buntan-pc/buntan-pc/cpu/mcu_rev2.sv

// SPDX-License-Identifier: MIT
/*
 * Copyright (c) 2026 Kota UCHIDA
 */
`include "common.sv"

module mcu_rev2#(
  parameter CLOCK_HZ = 27_000_000,
  parameter UART_BAUD = 115200
) (
  input rst, clk, uart_rx, uart2_rx, uart3_rx,
  output uart_tx, uart2_tx, uart3_tx,
  output [`ADDR_WIDTH-1:0] dmem_addr,
  output dmem_wen, dmem_byt,
  input  [15:0] dmem_rdata_io, // メモリ読み込みデータ（IO 領域）
  output [15:0] dmem_wdata,    // メモリ書き込みデータ（全領域）
  output [17:0] uart_recv_data,
  output [`ADDR_WIDTH-1:0] img_pmem_size,
  input  clk125,
  output logic spk_on,// DAC をスピーカーへ接続するかどうかを制御
  input  adc_cmp,     // ADC のコンパレータ出力
  output adc_sh_on,   // ADC のサンプル&ホールドスイッチ制御
  output [2:0] adc_sel,  // ADC のチャンネル選択
  output [7:0] adc_vref, // ADC の DAC 入力
  output logic [8:0] uf_xadr,
  output logic [5:0] uf_yadr,
  output logic uf_xe, uf_ye, uf_se, uf_erase, uf_prog, uf_nvstr,
  output logic [31:0] uf_din,
  input  [31:0] uf_dout,
  output spi_cs,
  output spi_sclk, spi_mosi,
  input  spi_miso,
  inout  i2c_scl, i2c_sda
);

localparam DMEM_GVAR_START = `ADDR_WIDTH'h0100;
localparam KEY_ROW_FOR_DEBUG = 0;
localparam KEY_COL_FOR_DEBUG = 0;

// CPU コア
logic [`ADDR_WIDTH-1:0] cpu_dmem_addr, cpu_dmem_addr_d, cpu_pmem_addr, pmem_addr;
logic [15:0] cpu_dmem_rdata, cpu_dmem_wdata;
logic [17:0] cpu_pmem_rdata, cpu_pmem_wdata;
logic cpu_dmem_ren, cpu_dmem_wen, cpu_dmem_byt, cpu_irq;
logic cpu_rst, cpu_pmem_wenh, cpu_pmem_wenl, pmem_wenh, pmem_wenl;

logic [17:0] recv_data, pmem_wdata;
logic [`ADDR_WIDTH-1:0] img_recv_addr, pmem_size, dmem_size;
logic [15:0] dmem_rdata_mem, dmem_rdata_mem_d;

assign uart_recv_data = recv_data;
assign img_pmem_size = pmem_size;

typedef enum logic [2:0] {
  IMG_RECV_WAIT, // メモリイメージ受信開始（55 AA）を待っている
  IMG_RECV_META, // メタデータ（データサイズなど）受信中
  IMG_RECV_PMEM, // pmem 受信中
  IMG_RECV_DMEM, // dmem 受信中
  IMG_RECV_FIN   // 終了処理
} img_recv_state_t;
img_recv_state_t img_recv_state;

// 0: 最上位バイトを待っている
// 2: 最下位バイトを待っている
logic [1:0] recv_byte_phase;

logic recv_data_v, recv_compl, uart_rx_ready;

//localparam CLK_DIV = 27_000_000 << 1;
//localparam CLK_DIV = 27_000_000 >> 1;
//localparam CLK_DIV = 27_000_000;
localparam CLK_DIV = 1;
logic [25:0] clk_div_cnt;
logic clk_div, cpu_clk;

always @(posedge rst, posedge clk) begin
  if (rst)
    clk_div_cnt <= 0;
  else if (clk_div_cnt == CLK_DIV - 1)
    clk_div_cnt <= 0;
  else
    clk_div_cnt <= clk_div_cnt + 1;
end

always @(posedge rst, posedge clk) begin
  if (rst)
    clk_div <= 0;
  else if (clk_div_cnt == CLK_DIV - 1)
    clk_div <= 0;
  else if (clk_div_cnt == (CLK_DIV >> 1))
    clk_div <= 1;
end

always @(posedge rst, posedge clk) begin
  if (rst)
    dmem_rdata_mem_d <= 0;
  else if (clk_div_cnt == (CLK_DIV >> 1) + 1)
    dmem_rdata_mem_d <= dmem_rdata_mem;
end

assign cpu_clk = CLK_DIV >= 2 ? clk_div : clk;
assign cpu_rst = rst | ~recv_compl;

always @(posedge cpu_clk, posedge rst) begin
  if (rst)
    cpu_dmem_addr_d <= `ADDR_WIDTH'd0;
  else
    cpu_dmem_addr_d <= cpu_dmem_addr;
end

cpu#(.CLOCK_HZ(CLOCK_HZ)) cpu(
  .rst(cpu_rst),
  .clk(cpu_clk),
  .irq(cpu_irq),
  .dmem_ren(cpu_dmem_ren),
  .dmem_wen(cpu_dmem_wen),
  .dmem_byt(cpu_dmem_byt),
  .dmem_addr(cpu_dmem_addr),
  .dmem_rdata(cpu_dmem_rdata),
  .dmem_wdata(cpu_dmem_wdata),
  .pmem_wenh(cpu_pmem_wenh),
  .pmem_wenl(cpu_pmem_wenl),
  .pmem_addr(cpu_pmem_addr),
  .pmem_rdata(cpu_pmem_rdata),
  .pmem_wdata(cpu_pmem_wdata)
);

// データメモリ
dmem dmem(
  .rst(rst),
  .clk(clk),
  .addr(dmem_addr),
  .wen(dmem_wen),
  .byt(dmem_byt),
  .data_in(dmem_wdata),
  .data_out(dmem_rdata_mem)
);

// プログラムメモリ
pmem pmem(
  .rst(rst),
  .clk(clk),
  .addr(pmem_addr),
  .wenh(pmem_wenh),
  .wenl(pmem_wenl),
  .data_in(pmem_wdata),
  .data_out(cpu_pmem_rdata)
);

// MCU 内蔵周辺機能：カウントダウンタイマ
logic cdtimer_to, load_cdtimer, cdtimer_ie;
logic [15:0] data_memreg, data_reg, cdtimer_cnt;

cdtimer#(.PERIOD(CLOCK_HZ/1000)) cdtimer(
  .rst(cpu_rst),
  .clk(clk),
  .load(load_cdtimer),
  .data(dmem_wdata),
  .counter(cdtimer_cnt),
  .timeout(cdtimer_to)
);

assign load_cdtimer = cpu_dmem_wen & cpu_dmem_addr === `ADDR_WIDTH'h002;

always @(posedge clk, posedge cpu_rst) begin
  if (cpu_rst)
    cdtimer_ie <= 1'b0;
  else if (cpu_dmem_wen && cpu_dmem_addr === `ADDR_WIDTH'h004)
    cdtimer_ie <= cpu_dmem_wdata[1];
end

// MCU 内蔵周辺機能：UART
logic [7:0] uart_rx_byte, uart_tx_byte;
logic uart_rd, uart_rx_full, uart_wr, uart_tx_ready, uart_ie;
logic img_recv, end_img_recv;

uart_mux#(.CLOCK_HZ(CLOCK_HZ), .BAUD(UART_BAUD), .TIM_WIDTH(8)) uart_mux(
  .rst(rst),
  .clk(clk),
  .rx(uart_rx),
  .tx(uart_tx),
  .rx_data(uart_rx_byte),
  .tx_data(uart_tx_byte),
  .rd(uart_rd),
  .rx_full(uart_rx_full),
  .wr(uart_wr),
  .tx_ready(uart_tx_ready),
  .img_recv(img_recv),
  .end_img_recv(end_img_recv)
);

assign uart_rd = uart_rx_full;
assign uart_wr = cpu_dmem_wen & cpu_dmem_addr === `ADDR_WIDTH'h006;
assign uart_tx_byte = cpu_dmem_wdata[7:0];
assign end_img_recv = img_recv_state == IMG_RECV_FIN;

always @(posedge clk, posedge rst) begin
  if (rst)
    uart_ie <= 1'b0;
  else if (cpu_dmem_wen && cpu_dmem_addr === `ADDR_WIDTH'h008)
    uart_ie <= cpu_dmem_wdata[1];
end

// MCU 内蔵周辺機能：UART2
logic [7:0] uart2_rx_byte, uart2_tx_byte;
logic uart2_rd, uart2_rx_full, uart2_wr, uart2_tx_ready, uart2_ie;

uart#(.CLOCK_HZ(CLOCK_HZ), .BAUD(9600), .TIM_WIDTH(12)) uart2(
  .rst(rst),
  .clk(clk),
  .rx(uart2_rx),
  .tx(uart2_tx),
  .rx_data(uart2_rx_byte),
  .tx_data(uart2_tx_byte),
  .rd(uart2_rd),
  .rx_full(uart2_rx_full),
  .wr(uart2_wr),
  .tx_ready(uart2_tx_ready)
);

assign uart2_rd = cpu_dmem_ren & cpu_dmem_addr_d === `ADDR_WIDTH'h02C;
assign uart2_wr = cpu_dmem_wen & cpu_dmem_addr === `ADDR_WIDTH'h02C;
assign uart2_tx_byte = cpu_dmem_wdata[7:0];

always @(posedge clk, posedge rst) begin
  if (rst)
    uart2_ie <= 1'b0;
  else if (cpu_dmem_wen && cpu_dmem_addr === `ADDR_WIDTH'h02E)
    uart2_ie <= cpu_dmem_wdata[1];
end

// MCU 内蔵周辺機能：UART3
logic [7:0] uart3_rx_byte, uart3_tx_byte;
logic uart3_rd, uart3_rx_full, uart3_wr, uart3_tx_ready, uart3_ie;

uart#(.CLOCK_HZ(CLOCK_HZ), .BAUD(9600), .TIM_WIDTH(12)) uart3(
  .rst(rst),
  .clk(clk),
  .rx(uart3_rx),
  .tx(uart3_tx),
  .rx_data(uart3_rx_byte),
  .tx_data(uart3_tx_byte),
  .rd(uart3_rd),
  .rx_full(uart3_rx_full),
  .wr(uart3_wr),
  .tx_ready(uart3_tx_ready)
);

assign uart3_rd = cpu_dmem_ren & cpu_dmem_addr_d === `ADDR_WIDTH'h030;
assign uart3_wr = cpu_dmem_wen & cpu_dmem_addr === `ADDR_WIDTH'h030;
assign uart3_tx_byte = cpu_dmem_wdata[7:0];

always @(posedge clk, posedge rst) begin
  if (rst)
    uart3_ie <= 1'b0;
  else if (cpu_dmem_wen && cpu_dmem_addr === `ADDR_WIDTH'h02E)
    uart3_ie <= cpu_dmem_wdata[1];
end

// MCU 内蔵周辺機能：ADC
logic [7:0] adc_result;
logic [7:0] vref_for_adc, vref_for_spk;
logic en_adc; // ADC 有効化（無効状態では DAC がスピーカー用になる）

adc_rev2#(.CLOCK_HZ(CLOCK_HZ)) adc(
  .rst(rst),
  .clk(clk),
  .clk125(clk125),
  .adc_cmp(adc_cmp),
  .adc_sh_on(adc_sh_on),
  .adc_sel(adc_sel),
  .adc_vref(vref_for_adc),
  .adc_result(adc_result)
);

assign adc_vref = en_adc ? vref_for_adc : vref_for_spk;

always @(posedge clk, posedge rst) begin
  if (rst) begin
    en_adc <= 1'b1;
    spk_on <= 1'b0;
  end
  else if (cpu_dmem_wen && cpu_dmem_addr === `ADDR_WIDTH'h00C) begin
    vref_for_spk <= cpu_dmem_wdata[7:0];
    en_adc <= cpu_dmem_wdata[8];
    spk_on <= cpu_dmem_wdata[9];
  end
end

// MCU 内蔵周辺機能：ユーザーフラッシュ
always @(posedge clk, posedge cpu_rst) begin
  if (cpu_rst) begin
    uf_xadr <= 0;
    uf_yadr <= 0;
    {uf_nvstr, uf_prog, uf_erase, uf_se, uf_ye, uf_xe} <= 0;
    uf_din <= 0;
  end
  else if (cpu_dmem_wen)
    case (cpu_dmem_addr)
      `ADDR_WIDTH'h010: uf_xadr <= cpu_dmem_wdata[8:0];
      `ADDR_WIDTH'h012: uf_yadr <= cpu_dmem_wdata[5:0];
      `ADDR_WIDTH'h014: {uf_nvstr, uf_prog, uf_erase, uf_se, uf_ye, uf_xe} <= cpu_dmem_wdata[5:0];
      `ADDR_WIDTH'h018: uf_din[15:0] <= cpu_dmem_wdata;
      `ADDR_WIDTH'h01A: uf_din[31:16] <= cpu_dmem_wdata;
      `ADDR_WIDTH'h01C: ; // cannot write to df_uout
      `ADDR_WIDTH'h01E: ; // cannot write to df_uout
    endcase
end

// MCU 内蔵周辺機能：SPI
logic spi_tx_start, spi_tx_ready, spi_cs_reg;
logic [7:0] spi_rx_data;

assign spi_tx_start = cpu_dmem_wen & cpu_dmem_addr === `ADDR_WIDTH'h020;
assign spi_cs = spi_cs_reg;

spi#(.CLOCK_HZ(CLOCK_HZ), .BAUD(100_000)) spi(
  .rst(rst),
  .clk(clk),
  .sclk(spi_sclk),
  .mosi(spi_mosi),
  .miso(spi_miso),
  .tx_data(cpu_dmem_wdata[7:0]),
  .rx_data(spi_rx_data),
  .tx_start(spi_tx_start),
  .tx_ready(spi_tx_ready)
);

always @(posedge rst, posedge clk) begin
  if (rst)
    spi_cs_reg <= 1;
  else if (cpu_dmem_wen & cpu_dmem_addr === `ADDR_WIDTH'h022)
    spi_cs_reg <= cpu_dmem_wdata[1];
end

// MCU 内蔵周辺機能：I2C
logic i2c_data_wen; // I2C データレジスタへの書き込みタイミング
logic i2c_tx_start, i2c_tx_start_d, i2c_tx_ready;
logic [7:0] i2c_tx_data, i2c_rx_data;
logic i2c_addr_rw; // アドレスの最下位ビットを保持
logic i2c_rw; // 1 バイトごとの読み書き方向制御
logic i2c_cnd_start, i2c_cnd_stop;
logic i2c_rx_ack;

// I2C 通信の状態
typedef enum logic [1:0] {
  ADDR,  // アドレス送信開始待ち（待機）
  DATA,  // データ送受信開始待ち
  START, // データ送受信開始
  WAIT   // データ送受信完了待ち
} i2c_state_t;
i2c_state_t i2c_state;

i2c#(.CLOCK_HZ(CLOCK_HZ)) i2c(
  .rst(rst),
  .clk(clk),
  .scl(i2c_scl),
  .sda(i2c_sda),
  .rw(i2c_rw),
  .cnd_start(i2c_cnd_start),
  .cnd_stop(i2c_cnd_stop),
  .tx_data(i2c_tx_data),
  .rx_data(i2c_rx_data),
  .tx_start(i2c_tx_start_d),
  .tx_ready(i2c_tx_ready),
  .tx_ack(1'b0),
  .rx_ack(i2c_rx_ack)
);

assign i2c_data_wen = cpu_dmem_wen & (cpu_dmem_addr === `ADDR_WIDTH'h028);
assign i2c_tx_start = (i2c_state == ADDR | i2c_state == DATA) & i2c_data_wen;

always @(posedge rst, posedge clk) begin
  if (rst)
    i2c_state <= ADDR;
  else if ((i2c_state == ADDR | i2c_state == DATA) & i2c_tx_start)
    i2c_state <= START;
  else if (i2c_state == DATA & i2c_cnd_stop)
    i2c_state <= ADDR;
  else if (i2c_state == START & ~i2c_tx_ready)
    i2c_state <= WAIT;
  else if (i2c_state == WAIT & i2c_tx_ready)
    i2c_state <= DATA;
end

always @(posedge rst, posedge clk) begin
  if (rst)
    i2c_cnd_start <= 0;
  else if (i2c_state == ADDR)
    i2c_cnd_start <= 1;
  else if (i2c_state == WAIT & i2c_tx_ready)
    i2c_cnd_start <= 0;
end

always @(posedge rst, posedge clk) begin
  if (rst)
    i2c_cnd_stop <= 0;
  else if (cpu_dmem_wen & cpu_dmem_addr === `ADDR_WIDTH'h02A)
    i2c_cnd_stop <= cpu_dmem_wdata[2];
  else if (~i2c_tx_ready)
    i2c_cnd_stop <= 0;
end

always @(posedge rst, posedge clk) begin
  if (rst)
    i2c_tx_start_d <= 0;
  else
    i2c_tx_start_d <= i2c_tx_start;
end

always @(posedge rst, posedge clk) begin
  if (rst)
    i2c_tx_data <= 8'd0;
  else if (i2c_data_wen)
    i2c_tx_data <= cpu_dmem_wdata[7:0];
end

always @(posedge rst, posedge clk) begin
  if (rst)
    i2c_addr_rw <= 0;
  else if (i2c_state == ADDR & i2c_data_wen)
    i2c_addr_rw <= cpu_dmem_wdata[0]; // 1 = read
end

always @(posedge rst, posedge clk) begin
  if (rst)
    i2c_rw <= 0;
  else if (i2c_state == ADDR)
    i2c_rw <= 0; // アドレスバイトは必ず write 方向
  else if (i2c_state == DATA)
    i2c_rw <= i2c_addr_rw; // データバイトは i2c_addr_rw の設定に従う
end

// MCU 内蔵周辺機能のメモリマップ
function [15:0] dmem_rdata_mux(
    input [`ADDR_WIDTH-1:0] dmem_addr,
    input [15:0] dmem_rdata_mem,
    input [15:0] dmem_rdata_io);
  casex (dmem_addr)
    `ADDR_WIDTH'h002:       return cdtimer_cnt;
    `ADDR_WIDTH'h004:       return {14'd0, cdtimer_ie, cdtimer_to};
    `ADDR_WIDTH'h006:       return {8'd0, recv_data[7:0]};
    `ADDR_WIDTH'h008:       return {13'd0, uart_tx_ready, uart_ie, uart_rx_ready};
    `ADDR_WIDTH'h00A:       return {8'd0, adc_result};
    `ADDR_WIDTH'h010:       return {7'd0, uf_xadr};
    `ADDR_WIDTH'h012:       return {10'd0, uf_yadr};
    `ADDR_WIDTH'h014:       return {10'd0, uf_nvstr, uf_prog, uf_erase, uf_se, uf_ye, uf_xe};
    `ADDR_WIDTH'h018:       return uf_din[15:0];
    `ADDR_WIDTH'h01A:       return uf_din[31:16];
    `ADDR_WIDTH'h01C:       return uf_dout[15:0];
    `ADDR_WIDTH'h01E:       return uf_dout[31:16];
    `ADDR_WIDTH'h020:       return {8'd0, spi_rx_data};
    `ADDR_WIDTH'h022:       return {14'd0, spi_cs, spi_tx_ready};
    `ADDR_WIDTH'h024:       return 16'd0;
    `ADDR_WIDTH'h026:       return 16'd0;
    `ADDR_WIDTH'h028:       return {8'd0, i2c_rx_data};
    `ADDR_WIDTH'h02A:       return {12'd0, i2c_rx_ack, i2c_cnd_stop, i2c_tx_ready, i2c_addr_rw};
    `ADDR_WIDTH'h02C:       return {8'd0, uart2_rx_byte};
    `ADDR_WIDTH'h02E:       return {13'd0, uart2_tx_ready, uart2_ie, uart2_rx_full};
    `ADDR_WIDTH'h030:       return {8'd0, uart3_rx_byte};
    `ADDR_WIDTH'h032:       return {13'd0, uart3_tx_ready, uart3_ie, uart3_rx_full};
    `ADDR_WIDTH'b1xxx_xxxx: return dmem_rdata_io;
    default:                return CLK_DIV >= 2 ? dmem_rdata_mem_d : dmem_rdata_mem;
  endcase
endfunction

// 信号結線
assign dmem_wen = (img_recv_state == IMG_RECV_WAIT & cpu_dmem_wen)
                | (img_recv_state == IMG_RECV_DMEM & img_recv_addr < DMEM_GVAR_START + dmem_size);
assign dmem_byt = img_recv_state == IMG_RECV_WAIT & cpu_dmem_byt;
assign dmem_addr = recv_compl ? cpu_dmem_addr : img_recv_addr;
assign dmem_wdata = img_recv_state == IMG_RECV_DMEM ? recv_data[15:0] : cpu_dmem_wdata;
assign pmem_addr = recv_compl ? cpu_pmem_addr : img_recv_addr;
assign pmem_wenh = (img_recv_state == IMG_RECV_WAIT & cpu_pmem_wenh)
                 | (img_recv_state == IMG_RECV_PMEM & img_recv_addr < pmem_size);
assign pmem_wenl = (img_recv_state == IMG_RECV_WAIT & cpu_pmem_wenl)
                 | (img_recv_state == IMG_RECV_PMEM & img_recv_addr < pmem_size);
assign pmem_wdata = img_recv_state == IMG_RECV_PMEM ? recv_data : cpu_pmem_wdata;
assign cpu_dmem_rdata = dmem_rdata_mux(cpu_dmem_addr_d, dmem_rdata_mem, dmem_rdata_io);
assign cpu_irq  = (cdtimer_to & cdtimer_ie) | (uart_rx_ready & uart_ie) | (uart2_rx_full & uart2_ie);

always @(posedge rst, posedge clk) begin
  if (rst)
    img_recv_state <= IMG_RECV_WAIT;
  else if (img_recv_state == IMG_RECV_WAIT & img_recv)
    img_recv_state <= IMG_RECV_META;
  else if (img_recv_state == IMG_RECV_META & img_recv_addr == `ADDR_WIDTH'd2)
    img_recv_state <= IMG_RECV_PMEM;
  else if (img_recv_state == IMG_RECV_PMEM & img_recv_addr == pmem_size)
    img_recv_state <= IMG_RECV_DMEM;
  else if (img_recv_state == IMG_RECV_DMEM & img_recv_addr == DMEM_GVAR_START + dmem_size)
    img_recv_state <= IMG_RECV_FIN;
  else if (img_recv_state == IMG_RECV_FIN)
    img_recv_state <= IMG_RECV_WAIT;
end

always @(posedge rst, posedge clk) begin
  if (rst | recv_compl) begin
    pmem_size <= `ADDR_WIDTH'd0;
    dmem_size <= `ADDR_WIDTH'd0;
  end
  else if (recv_data_v && img_recv_state == IMG_RECV_META)
    if (img_recv_addr == `ADDR_WIDTH'd0)
      pmem_size <= recv_data[`ADDR_WIDTH-1:0];
    else if (img_recv_addr == `ADDR_WIDTH'd1)
      dmem_size <= recv_data[`ADDR_WIDTH-1:0];
end

always @(posedge rst, posedge clk) begin
  if (rst | recv_compl)
    recv_byte_phase <= 2'd0;
  else if (recv_data_v)
    recv_byte_phase <= 2'd0;
  else if (uart_rx_full)
    recv_byte_phase <= recv_byte_phase + 2'd1;
end

// recv_data は UART から受信した直近 18 ビットを記憶する
always @(posedge rst, posedge clk) begin
  if (rst)
    recv_data <= 18'd0;
  else if (uart_rx_full)
    recv_data <= {recv_data[9:0], uart_rx_byte};
end

// recv_data_v は命令の受信が完了したら 1 になる
always @(posedge rst, posedge clk) begin
  if (rst | img_recv_state == IMG_RECV_WAIT)
    recv_data_v <= 1'b0;
  else if (img_recv_state == IMG_RECV_META)
    recv_data_v <= uart_rx_full & recv_byte_phase == 2'd1;
  else if (img_recv_state == IMG_RECV_PMEM)
    recv_data_v <= uart_rx_full & recv_byte_phase == 2'd2;
  else if (img_recv_state == IMG_RECV_DMEM)
    recv_data_v <= uart_rx_full & recv_byte_phase == 2'd1;
end

// img_recv_addr は命令の受信が完了するたびにインクリメントされる
always @(posedge rst, posedge clk) begin
  if (rst | img_recv_state == IMG_RECV_WAIT)
    img_recv_addr <= `ADDR_WIDTH'd0;
  else if (img_recv_state == IMG_RECV_META && img_recv_addr == `ADDR_WIDTH'd2)
    img_recv_addr <= `ADDR_WIDTH'd0;
  else if (img_recv_state == IMG_RECV_PMEM && img_recv_addr == pmem_size)
    img_recv_addr <= DMEM_GVAR_START;
  else if (img_recv_state == IMG_RECV_DMEM && img_recv_addr == DMEM_GVAR_START + dmem_size)
    img_recv_addr <= `ADDR_WIDTH'd0;
  else if (recv_data_v)
    img_recv_addr <= img_recv_addr +
      (img_recv_state == IMG_RECV_DMEM ? `ADDR_WIDTH'd2 : `ADDR_WIDTH'd1);
end

always @(posedge rst, posedge clk) begin
  if (rst)
    recv_compl <= 1'b1;
  else if (img_recv_state == IMG_RECV_FIN)
    recv_compl <= 1'b1;
  else if (img_recv)
    recv_compl <= 1'b0;
end

always @(posedge cpu_rst, posedge clk) begin
  if (cpu_rst)
    uart_rx_ready <= 1'b0;
  else if (uart_rx_full)
    uart_rx_ready <= 1'b1;
  else if (cpu_dmem_ren & cpu_dmem_addr_d === `ADDR_WIDTH'h006)
    uart_rx_ready <= 1'b0;
  else if (cpu_dmem_wen & cpu_dmem_addr === `ADDR_WIDTH'h008)
    uart_rx_ready <= cpu_dmem_wdata[0];
end

endmodule
