buntan-pc/buntan-pc/ucc/ast.c

// SPDX-License-Identifier: MIT
/*
 * Copyright (c) 2024 Kota UCHIDA
 */
#include "ast.h"

#include <assert.h>
#include <stdio.h>
#include <stdlib.h>
#include <string.h>

#include "symbol.h"
#include "token.h"

struct Type *TYPE_INT;

void Locate(char *p);

struct Node *NewNode(enum NodeKind kind, struct Token *token) {
  static int last_index = 0;
  struct Node *n = malloc(sizeof(struct Node));
  n->kind = kind;
  n->index = last_index++;
  n->token = token;
  n->next = n->lhs = n->rhs = n->cond = NULL;
  n->type = NULL;
  n->scope = NULL;
  return n;
}

struct Node *NewNodeInteger(struct Token *token) {
  struct Node *n = NewNode(kNodeInteger, token);
  n->type = TYPE_INT;
  return n;
}

struct Node *NewNodeBinOp(enum NodeKind kind, struct Token *op,
                          struct Node *lhs, struct Node *rhs) {
  struct Node *n = NewNode(kind, op);
  n->lhs = lhs;
  n->rhs = rhs;
  return n;
}

struct Type *DecideBinOpType(struct Type *lhs, struct Type *rhs) {
  if (lhs == NULL || rhs == NULL) {
    return NULL;
  }

  struct Type *t = NULL;
  if (lhs->kind == kTypeChar && rhs->kind == kTypeChar) {
    t = TYPE_INT;
  } else if (lhs->kind == kTypeChar) { // rhs は int
    t = rhs;
  } else if (rhs->kind == kTypeChar) { // lhs は int
    t = lhs;
  } else { // 両辺が int
    if (lhs->attr & TYPE_ATTR_SIGNED) {
      // lhs が signed のとき、全体の型は rhs の signed/unsigned により決まる
      t = rhs;
    } else {
      // lhs が unsigned のとき、全体の型は unsigned になる
      t = lhs;
    }
  }
  return t;
}

struct Node *Program(struct ParseContext *ctx) {
  struct Token *token_list = cur_token;
  ctx->pass = kPPInit;
  while (ExternalDeclaration(ctx));

  cur_token = token_list;
  ctx->pass = kPPMain;

  TYPE_INT = NewType(kTypeInt);
  TYPE_INT->attr = TYPE_ATTR_SIGNED;

  struct Node *head = ExternalDeclaration(ctx);
  struct Node *n = head;
  while (n) {
    n->next = ExternalDeclaration(ctx);
    n = n->next;
  }
  return head;
}

struct Node *ExternalDeclaration(struct ParseContext *ctx) {
  struct Node *tspec = TypeSpecNode();

  if (!tspec) {
    return NULL;
  }

  struct Token *id;
  if (tspec->type->kind == kTypePtr &&
      tspec->type->base->kind == kTypeFunc) {
    id = tspec->type->base->id;
  } else {
    id = Expect(kTokenId);
  }
  if (Consume('(')) {
    return FunctionDefinition(ctx, tspec, id);
  } else {
    return VariableDefinition(ctx, tspec, id);
  }
}

struct Node *FunctionDefinition(struct ParseContext *ctx,
                                struct Node *tspec, struct Token *id) {
  struct Node *func_def;
  if (ctx->pass == kPPMain) {
    struct Symbol *func_sym = FindSymbol(ctx->scope, id);
    assert(func_sym != NULL);
    func_def = func_sym->def;
  } else {
    if (FindSymbol(ctx->scope, id)) {
      fprintf(stderr, "symbol redefined\n");
      Locate(id->raw);
      exit(1);
    }
    func_def = NewNode(kNodeDefFunc, id);
    func_def->lhs = tspec;
    struct Symbol *func_sym = NewSymbol(kSymFunc, id);
    func_sym->def = func_def;
    func_sym->type = NewFuncType(tspec->type, id);
    AppendSymbol(ctx->scope->syms, func_sym);
  }

  ctx->scope = EnterScope(ctx->scope);
  func_def->scope = ctx->scope;

  struct Node *params = ParameterList();
  Expect(')');
  for (struct Node *param = params; param; param = param->next) {
    if (param->token->kind == kTokenEllipsis) {
      break;
    }
    struct Symbol *sym = NewSymbol(kSymLVar, param->lhs->token);
    sym->type = param->type;
    sym->offset = ctx->scope->var_offset;
    ctx->scope->var_offset += 2;
    AppendSymbol(ctx->scope->syms, sym);
  }
  func_def->cond = params;

  struct Node *func_body = Block(ctx);
  func_def->rhs = func_body;

  // void 関数で、最後が return で終わっていなければ追加
  if (tspec->type->kind == kTypeVoid) {
    struct Node *last_node = func_body->rhs;
    if (last_node) {
      while (last_node->next) {
        last_node = last_node->next;
      }
      if (last_node->kind != kNodeReturn) {
        last_node->next = NewNode(kNodeReturn, NULL);
      }
    } else {
      func_body->rhs = NewNode(kNodeReturn, NULL);
    }
  }

  ctx->scope = ctx->scope->parent;
  return func_def;
}

struct Node *VariableInitializer(struct ParseContext *ctx, struct Symbol *sym) {
  struct Token *br = Consume('{');
  if (!br) {
    return Expression(ctx);
  }

  if (sym->type->kind != kTypeArray) {
    fprintf(stderr, "initializer list is allowed only for arrays\n");
    Locate(br->raw);
    exit(1);
  }

  struct Node *init = NewNode(kNodeIList, br);
  struct Node *n = init;
  uint16_t i = 0;
  while (!Consume('}')) {
    struct Token *n_start = cur_token;
    if (Consume(',')) {
      fprintf(stderr, "expression required\n");
      Locate(n_start->raw);
      exit(1);
    }
    n->next = Expression(ctx);
    n = n->next;
    if (++i > sym->type->len) {
      fprintf(stderr, "too many initializer\n");
      Locate(n_start->raw);
      exit(1);
    }
    if (!Consume(',')) {
      Expect('}');
      break;
    }
  }
  init->rhs = init->next;
  init->next = NULL;
  return init;
}

struct Node *VariableDefinition(struct ParseContext *ctx,
                                struct Node *tspec, struct Token *id) {
  if (Consume('[')) {
    struct Token *len = Expect(kTokenInteger);
    Expect(']');
    struct Type *t = NewType(kTypeArray);
    t->len = len->value.as_int;
    t->base = tspec->type;
    tspec->type = t;
  }

  enum SymbolKind sym_kind = ctx->scope->parent ? kSymLVar : kSymGVar;
  struct Node *def;
  struct Symbol *sym;
  if (ctx->pass == kPPMain && sym_kind == kSymGVar) {
    sym = FindSymbol(ctx->scope, id);
    assert(sym != NULL);
    def = sym->def;
  } else {
    if (sym_kind == kSymGVar && FindSymbol(ctx->scope, id)) {
      fprintf(stderr, "symbol redefined\n");
      Locate(id->raw);
      exit(1);
    }
    def = NewNode(kNodeDefVar, tspec->token);
    def->type = tspec->type;
    def->lhs = NewNode(kNodeId, id);
    sym = NewSymbol(sym_kind, id);
    sym->def = def;
    sym->type = def->type;
    sym->offset = ctx->scope->var_offset;
    AppendSymbol(ctx->scope->syms, sym);
  }

  int attr_at = 0;
  if (Consume(kTokenAttr)) {
    struct Token *attr;
    Expect('(');
    Expect('(');
    if ((attr = Consume(kTokenId))) {
      if (strncmp(attr->raw, "at", attr->len) == 0) {
        if (sym->kind != kSymGVar) {
          fprintf(stderr, "'at' attribute can only be used with global variables\n");
          Locate(attr->raw);
          exit(1);
        }
        sym->attr |= SYM_ATTR_FIXED_ADDR;

        Expect('(');
        struct Token *addr = Expect(kTokenInteger);
        sym->offset = addr->value.as_int;
        Expect(')');
        attr_at = 1;
      } else {
        fprintf(stderr, "unknown attribute\n");
        Locate(attr->raw);
        exit(1);
      }
    }
    Expect(')');
    Expect(')');
  }

  if (!attr_at) {
    size_t mem_size = (SizeofType(def->type) + 1) & ~((size_t)1);
    ctx->scope->var_offset += mem_size;
  }

  if (Consume('=')) {
    def->rhs = VariableInitializer(ctx, sym);
  }
  Expect(';');

  return def;
}

struct Node *Block(struct ParseContext *ctx) {
  struct Token *brace = Consume('{');
  if (brace == NULL) {
    return NULL;
  }

  struct Node *block = NewNode(kNodeBlock, brace);
  block->scope = ctx->scope;

  struct Node *node = block;
  while (Consume('}') == NULL) {
    if ((node->next = InnerDeclaration(ctx))) {
    } else if ((node->next = Statement(ctx))) {
    } else {
      fprintf(stderr, "either declaration or statement is expected\n");
      Locate(cur_token->raw);
      exit(1);
    }

    node = node->next;
  }
  block->rhs = block->next;
  block->next = NULL;

  return block;
}

struct Node *InnerDeclaration(struct ParseContext *ctx) {
  struct Node *ed = ExternalDeclaration(ctx);
  if (ed == NULL) {
    return NULL;
  }
  if (ed->kind == kNodeDefFunc) {
    fprintf(stderr, "inner func is not allowed\n");
    Locate(ed->token->raw);
    exit(1);
  }
  return ed;
}

struct Node *Statement(struct ParseContext *ctx) {
  struct Token *token;

  if ((token = Consume(kTokenReturn))) {
    struct Node *ret = NewNode(kNodeReturn, token);
    ret->lhs = Expression(ctx);
    Expect(';');
    return ret;
  }

  if ((token = Consume(kTokenIf))) {
    struct Node *if_ = NewNode(kNodeIf, token);
    Expect('(');
    if_->cond = Expression(ctx);
    Expect(')');
    if_->lhs = Statement(ctx);

    if ((token = Consume(kTokenElse))) {
      if_->rhs = Statement(ctx);
    }

    return if_;
  }

  if ((token = Consume(kTokenSwitch))) {
    struct Node *switch_ = NewNode(kNodeSwitch, token);
    Expect('(');
    switch_->cond = Expression(ctx);
    Expect(')');
    if (cur_token->kind != '{') {
      fprintf(stderr, "switch needs one block\n");
      Locate(cur_token->raw);
      exit(1);
    }
    switch_->rhs = Statement(ctx);

    return switch_;
  }

  if ((token = Consume(kTokenCase)) || (token = Consume(kTokenDefault))) {
    struct Node *case_ = NewNode(kNodeCase, token);
    // default は case_->cond == NULL
    if (token->kind == kTokenCase) {
      case_->cond = Primary(ctx);
    }
    Expect(':');
    return case_;
  }

  if ((token = Consume(kTokenFor))) {
    struct Node *for_ = NewNode(kNodeFor, token);
    Expect('(');
    for_->lhs = InitStatement(ctx);
    for_->cond = Expression(ctx);
    Expect(';');
    for_->lhs->next = Expression(ctx);
    Expect(')');
    for_->rhs = Statement(ctx);

    return for_;
  }

  if ((token = Consume(kTokenWhile))) {
    struct Node *while_ = NewNode(kNodeWhile, token);
    Expect('(');
    while_->cond = Expression(ctx);
    Expect(')');
    while_->rhs = Statement(ctx);

    return while_;
  }

  if ((token = Consume(kTokenBreak))) {
    Expect(';');
    return NewNode(kNodeBreak, token);
  }

  if ((token = Consume(kTokenContinue))) {
    Expect(';');
    return NewNode(kNodeContinue, token);
  }

  if (cur_token->kind == '{') {
    ctx->scope = EnterScope(ctx->scope);
    ctx->scope->var_offset = ctx->scope->parent->var_offset;
    struct Node *block = Block(ctx);
    ctx->scope = ctx->scope->parent;
    return block;
  }

  if ((token = Consume(kTokenAsm))) {
    struct Node *asm_ = NewNode(kNodeAsm, token);
    Expect('(');
    asm_->lhs = NewNode(kNodeString, Expect(kTokenString));
    while (Consume(kTokenString));
    Expect(')');
    Expect(';');
    return asm_;
  }

  struct Node *e = Expression(ctx);
  Expect(';');

  return e;
}

struct Node *InitStatement(struct ParseContext *ctx) {
  struct Node *n = InnerDeclaration(ctx);
  if (n == NULL) {
    n = Expression(ctx);
    Expect(';');
  }
  return n;
}

struct Node *Expression(struct ParseContext *ctx) {
  return Assignment(ctx);
}

struct Node *Assignment(struct ParseContext *ctx) {
  struct Node *node = LogicalOr(ctx);

  struct Token *op;
  if ((op = Consume('='))) {
    node = NewNodeBinOp(kNodeAssign, op, node, Assignment(ctx));
    node->type = node->lhs->type;
  } else if ((op = Consume(kTokenCompAssign + '+'))) {
    node = NewNodeBinOp(kNodeAssign, op, node,
                        NewNodeBinOp(kNodeAdd, op, node, Assignment(ctx)));
    node->type = node->lhs->type;
  } else if ((op = Consume(kTokenCompAssign + '-'))) {
    node = NewNodeBinOp(kNodeAssign, op, node,
                        NewNodeBinOp(kNodeSub, op, node, Assignment(ctx)));
    node->type = node->lhs->type;
  } else if ((op = Consume(kTokenCompAssign + '|'))) {
    node = NewNodeBinOp(kNodeAssign, op, node,
                        NewNodeBinOp(kNodeOr, op, node, Assignment(ctx)));
    node->type = node->lhs->type;
  } else if ((op = Consume(kTokenCompAssign + '^'))) {
    node = NewNodeBinOp(kNodeAssign, op, node,
                        NewNodeBinOp(kNodeXor, op, node, Assignment(ctx)));
    node->type = node->lhs->type;
  } else if ((op = Consume(kTokenCompAssign + '&'))) {
    node = NewNodeBinOp(kNodeAssign, op, node,
                        NewNodeBinOp(kNodeAnd, op, node, Assignment(ctx)));
    node->type = node->lhs->type;
  }

  return node;
}

struct Node *LogicalOr(struct ParseContext *ctx) {
  struct Node *node = LogicalAnd(ctx);

  struct Token *op;
  if ((op = Consume(kTokenOr))) {
    node = NewNodeBinOp(kNodeLOr, op, node, LogicalOr(ctx));
  }

  return node;
}

struct Node *LogicalAnd(struct ParseContext *ctx) {
  struct Node *node = BitwiseOr(ctx);

  struct Token *op;
  if ((op = Consume(kTokenAnd))) {
    node = NewNodeBinOp(kNodeLAnd, op, node, LogicalAnd(ctx));
  }

  return node;
}

struct Node *BitwiseOr(struct ParseContext *ctx) {
  struct Node *node = BitwiseXor(ctx);

  struct Token *op;
  if ((op = Consume('|'))) {
    node = NewNodeBinOp(kNodeOr, op, node, BitwiseOr(ctx));
    node->type = DecideBinOpType(node->lhs->type, node->rhs->type);
  }

  return node;
}

struct Node *BitwiseXor(struct ParseContext *ctx) {
  struct Node *node = BitwiseAnd(ctx);

  struct Token *op;
  if ((op = Consume('^'))) {
    node = NewNodeBinOp(kNodeXor, op, node, BitwiseXor(ctx));
    node->type = DecideBinOpType(node->lhs->type, node->rhs->type);
  }

  return node;
}

struct Node *BitwiseAnd(struct ParseContext *ctx) {
  struct Node *node = Equality(ctx);

  struct Token *op;
  if ((op = Consume('&'))) {
    node = NewNodeBinOp(kNodeAnd, op, node, BitwiseAnd(ctx));
    node->type = DecideBinOpType(node->lhs->type, node->rhs->type);
  }

  return node;
}

struct Node *Equality(struct ParseContext *ctx) {
  struct Node *node = Relational(ctx);

  struct Token *op;
  if ((op = Consume(kTokenEq))) {
    node = NewNodeBinOp(kNodeEq, op, node, Equality(ctx));
    node->type = TYPE_INT;
  } else if ((op = Consume(kTokenNEq))) {
    node = NewNodeBinOp(kNodeNEq, op, node, Equality(ctx));
    node->type = TYPE_INT;
  }

  return node;
}

struct Node *Relational(struct ParseContext *ctx) {
  struct Node *node = BitwiseShift(ctx);

  struct Token *op;
  if ((op = Consume('<'))) {
    node = NewNodeBinOp(kNodeLT, op, node, Relational(ctx));
    node->type = TYPE_INT;
  } else if ((op = Consume('>'))) {
    node = NewNodeBinOp(kNodeLT, op, Relational(ctx), node);
    node->type = TYPE_INT;
  } else if ((op = Consume(kTokenLE))) {
    node = NewNodeBinOp(kNodeLE, op, node, Relational(ctx));
    node->type = TYPE_INT;
  } else if ((op = Consume(kTokenGE))) {
    node = NewNodeBinOp(kNodeLE, op, Relational(ctx), node);
    node->type = TYPE_INT;
  }

  return node;
}

struct Node *BitwiseShift(struct ParseContext *ctx) {
  struct Node *node = Additive(ctx);

  struct Token *op;
  if ((op = Consume(kTokenRShift))) {
    node = NewNodeBinOp(kNodeRShift, op, node, BitwiseShift(ctx));
    node->type = node->lhs->type;
  } else if ((op = Consume(kTokenLShift))) {
    node = NewNodeBinOp(kNodeLShift, op, node, BitwiseShift(ctx));
    node->type = node->lhs->type;
  }

  return node;
}

struct Node *Additive(struct ParseContext *ctx) {
  struct Node *node = Multiplicative(ctx);

  struct Token *op;
  while (1) {
    if ((op = Consume('+'))) {
      node = NewNodeBinOp(kNodeAdd, op, node, Multiplicative(ctx));
      if (ctx->pass == kPPMain) {
        if (node->lhs->type->kind == kTypePtr) {
          node->type = node->lhs->type;
        } else {
          node->type = DecideBinOpType(node->lhs->type, node->rhs->type);
        }
      }
    } else if ((op = Consume('-'))) {
      node = NewNodeBinOp(kNodeSub, op, node, Multiplicative(ctx));
      if (ctx->pass == kPPMain) {
        if (node->lhs->type->kind == kTypePtr) {
          if (node->rhs->type->kind == kTypePtr) {
            node->type = TYPE_INT;
          } else {
            node->type = node->lhs->type;
          }
        } else {
          node->type = DecideBinOpType(node->lhs->type, node->rhs->type);
        }
      }
    } else {
      break;
    }
  }

  return node;
}

struct Node *Multiplicative(struct ParseContext *ctx) {
  struct Node *node = Cast(ctx);

  struct Token *op;
  if ((op = Consume('*'))) {
    node = NewNodeBinOp(kNodeMul, op, node, Multiplicative(ctx));
    node->type = DecideBinOpType(node->lhs->type, node->rhs->type);
  }

  return node;
}

struct Node *Cast(struct ParseContext *ctx) {
  struct Token *origin = cur_token;

  struct Token *op = Consume('(');
  if (!op) {
    return Unary(ctx);
  }

  struct Node *tspec = TypeSpecNode();
  if (!tspec) {
    cur_token = origin;
    return Unary(ctx);
  }

  Expect(')');
  struct Node *node = NewNodeBinOp(kNodeCast, op, tspec, Cast(ctx));
  node->type = tspec->type;

  return node;
}

struct Node *Unary(struct ParseContext *ctx) {
  struct Node *node;

  struct Token *op;
  if ((op = Consume(kTokenInc))) {
    node = NewNodeBinOp(kNodeInc, op, NULL, Unary(ctx));
    node->type = node->rhs->type;
  } else if ((op = Consume(kTokenDec))) {
    node = NewNodeBinOp(kNodeDec, op, NULL, Unary(ctx));
    node->type = node->rhs->type;
  } else if ((op = Consume('&'))) {
    node = NewNodeBinOp(kNodeRef, op, NULL, Cast(ctx));
    node->type = NewType(kTypePtr);
    node->type->base = node->rhs->type;
  } else if ((op = Consume('*'))) {
    node = NewNodeBinOp(kNodeDeref, op, NULL, Cast(ctx));
    if (ctx->pass == kPPMain) {
      node->type = node->rhs->type->base;
    }
  } else if ((op = Consume('-'))) {
    struct Token *zero_tk = NewToken(kTokenInteger, NULL, 0);
    zero_tk->value.as_int = 0;
    struct Node *zero = NewNodeInteger(zero_tk);
    node = NewNodeBinOp(kNodeSub, op, zero, Unary(ctx));
    node->type = node->rhs->type;
  } else if ((op = Consume('~'))) {
    node = NewNodeBinOp(kNodeNot, op, NULL, Cast(ctx));
    node->type = node->rhs->type;
  } else if ((op = Consume('!'))) {
    struct Token *zero_tk = NewToken(kTokenInteger, NULL, 0);
    zero_tk->value.as_int = 0;
    struct Node *zero = NewNodeInteger(zero_tk);
    node = NewNodeBinOp(kNodeEq, op, zero, Unary(ctx));
    node->type = node->rhs->type;
  } else {
    node = Postfix(ctx);
  }

  return node;
}

struct Node *Postfix(struct ParseContext *ctx) {
  struct Node *node = Primary(ctx);

  if (node->kind == kNodeId && strncmp(node->token->raw, "va_", 3) == 0) {
    char *func_name = node->token->raw + 3;
    int func_name_len = node->token->len - 3;
    if (strncmp(func_name, "arg", func_name_len) == 0) {
      Expect('(');
      struct Token *ap_tk = Expect(kTokenId);
      Expect(',');
      TypeSpecNode();
      Expect(')');

      struct Symbol *ap_sym = FindSymbol(ctx->scope, ap_tk);
      if (!ap_sym) {
        fprintf(stderr, "symbol not found\n");
        Locate(ap_tk->raw);
        exit(1);
      }

      struct Node *ap_node = NewNode(kNodeId, ap_tk);
      ap_node->type = ap_sym->type;

      // va_arg(ap, int) を *(ap++) に展開する
      node = NewNode(kNodeDeref, node->token);
      node->type = ap_node->type->base;
      node->rhs = NewNode(kNodeInc, node->token);
      node->rhs->lhs = ap_node;
      node->rhs->type = ap_node->type;
      return node;
    } else if (strncmp(func_name, "start", func_name_len) == 0) {
      Expect('(');
      struct Token *ap_tk = Expect(kTokenId);
      Expect(',');
      Expect(kTokenId);
      Expect(')');

      struct Symbol *ap_sym = FindSymbol(ctx->scope, ap_tk);
      if (!ap_sym) {
        fprintf(stderr, "symbol not found\n");
        Locate(ap_tk->raw);
        exit(1);
      }

      // ap の初期値は関数呼び出し直後の FP
      struct Node *ap_init = NewNode(kNodeFP, node->token);
      struct Node *ap = NewNode(kNodeId, ap_tk);
      ap->type = ap_sym->type;
      struct Node *assign = NewNodeBinOp(kNodeAssign, node->token, ap, ap_init);
      assign->type = ap->type;
      return assign;
    }
  }

  struct Token *op;
  while (1) {
    if ((op = Consume(kTokenInc))) {
      node = NewNodeBinOp(kNodeInc, op, node, NULL);
      node->type = node->lhs->type;
    } else if ((op = Consume(kTokenDec))) {
      node = NewNodeBinOp(kNodeDec, op, node, NULL);
      node->type = node->lhs->type;
    } else if ((op = Consume('['))) {
      struct Type *array_type = node->type;
      struct Node *ind = NewNodeBinOp(kNodeAdd, op, node, Expression(ctx));
      ind->type = array_type;
      Expect(']');

      node = NewNodeBinOp(kNodeDeref, op, NULL, ind);
      if (ctx->pass == kPPMain) {
        node->type = array_type->base;
      }
    } else if ((op = Consume('('))) {
      struct Token *id = node->token;
      node = NewNodeBinOp(kNodeCall, op, node, NULL);
      if (ctx->pass == kPPMain) {
        struct Symbol *func = FindSymbol(ctx->scope, id);
        if (!func) {
          fprintf(stderr, "symbol not found\n");
          Locate(id->raw);
          exit(1);
        }

        // 関数の戻り値型を取得
        if (func->kind == kSymFunc || func->kind == kSymBif) {
          node->type = func->def->lhs->type;
        } else if (func->kind == kSymLVar || func->kind == kSymGVar) {
          if (func->type->kind == kTypePtr) {
            node->type = func->type->base;
          } else {
            fprintf(stderr, "failed to determine the return type\n");
            Locate(node->token->raw);
            exit(1);
          }
        }
      }

      if (!Consume(')')) {
        node->rhs = Expression(ctx);
        struct Node *arg = node->rhs;
        while (Consume(',')) {
          arg->next = Expression(ctx);
          arg = arg->next;
        }
        Expect(')');
      }
    } else {
      break;
    }
  }

  return node;
}

struct Node *Primary(struct ParseContext *ctx) {
  struct Node *node = NULL;
  struct Token *tk;
  if ((tk = Consume('('))) {
    node = Expression(ctx);
    Expect(')');
  } else if ((tk = Consume(kTokenInteger))) {
    node = NewNodeInteger(tk);
  } else if ((tk = Consume(kTokenCharacter))) {
    node = NewNodeInteger(tk);
  } else if ((tk = Consume(kTokenString))) {
    node = NewNode(kNodeString, tk);
    node->type = NewType(kTypePtr);
    node->type->base = NewType(kTypeChar);

    // 文字列リテラルが連続する区間は 1 つの kNodeString ノードが担当する
    while (Consume(kTokenString));
  } else if ((tk = Consume(kTokenId))) {
    node = NewNode(kNodeId, tk);
    if (ctx->pass == kPPMain) {
      struct Symbol *sym = FindSymbol(ctx->scope, tk);
      if (!sym) {
        fprintf(stderr, "symbol not found\n");
        Locate(tk->raw);
        exit(1);
      }
      node->type = sym->type;
    }
  } else {
    node = NewNode(kNodeVoid, cur_token);
  }

  return node;
}

struct Type *TypeSpec() {
  struct Type *type = NULL;
  struct Token *token;

  if ((token = Consume(kTokenEllipsis))) {
    // 可変長引数
    return NewType(kTypeEllipsis);
  }

  // (un)signed が明示的に指定されたら 1
  int attr_signed = 0, attr_unsigned = 0;
  if ((token = Consume(kTokenSigned))) {
    attr_signed = 1;
  } else if ((token = Consume(kTokenUnsigned))) {
    attr_unsigned = 1;
  }

  if ((token = Consume(kTokenInt))) {
    type = NewType(kTypeInt);
  } else if ((token = Consume(kTokenChar))) {
    type = NewType(kTypeChar);
  } else if ((token = Consume(kTokenVoid))) {
    type = NewType(kTypeVoid);
  } else if ((token = Consume(kTokenVAList))) {
    type = NewType(kTypePtr);
    type->base = NewType(kTypeInt);
    // va_list はとりあえず int* としておく
  }

  if (!type) {
    if (attr_signed || attr_unsigned) {
      type = NewType(kTypeInt); // デフォルトで int
    } else {
      return NULL;
    }
  }

  if (attr_signed) {
    type->attr |= TYPE_ATTR_SIGNED;
  } else if (attr_unsigned) {
    // pass
  } else if (type->kind != kTypeChar) {
    type->attr |= TYPE_ATTR_SIGNED;
  }

  while (Consume('*')) {
    struct Type *t = NewType(kTypePtr);
    t->base = type;
    type = t;
  }

  if (Consume('(')) { // 関数ポインタ
    Expect('*');
    struct Token *id = Consume(kTokenId);
    Expect(')');
    Expect('(');

    type = NewType(kTypePtr);
    type->base = NewFuncType(type, id);

    struct Type *t = type->base;
    t->next = TypeSpec();
    while (Consume(',')) {
      t = t->next;
      t->next = TypeSpec();
      Consume(kTokenId); // パラメタ名は無視
    }

    Expect(')');
  }

  return type;
}

struct Node *TypeSpecNode() {
  struct Token *token = cur_token;
  struct Type *typ = TypeSpec();
  if (!typ) {
    return NULL;
  }
  struct Node *tspec = NewNode(kNodeTypeSpec, token);
  tspec->type = typ;
  return tspec;
}

struct Node *OneParameter() {
  struct Token *op;
  if ((op = Consume(kTokenEllipsis))) {
    // 可変長引数
    return NewNode(kNodePList, op);
  }

  struct Node *tspec = TypeSpecNode();
  if (!tspec) {
    return NULL;
  }

  struct Node *param = NewNode(kNodePList, tspec->token);
  param->type = tspec->type;
  struct Token *id;
  if (tspec->type->kind == kTypePtr &&
      tspec->type->base->kind == kTypeFunc) {
    id = tspec->type->base->id;
  } else {
    id = Expect(kTokenId);
  }
  param->lhs = NewNode(kNodeId, id);
  return param;
}

struct Node *ParameterList() {
  struct Node *param = OneParameter();
  if (!param) {
    return NULL;
  }

  struct Node *plist = param;

  while (Consume(',')) {
    param->next = OneParameter();
    param = param->next;
  }
  return plist;
}

static const char *node_kind_name[] = {
  "Integer",
  "Id",
  "Add",
  "Sub",
  "Mul",
  "Assign",
  "LT", // <
  "Inc",
  "Dec",
  "Eq",
  "NEq",
  "Ref",   // & exp
  "Deref", // * exp
  "LAnd",  // &&
  "LOr",   // ||
  "String",// string literal
  "And",   // &
  "Xor",   // ^
  "Or",    // |
  "Not",   // ~
  "RShift",// >>
  "LShift",// <<
  "Call",
  "ExprEnd",
  "DefFunc",
  "Block",
  "Return",
  "DefVar",
  "If",
  "For",
  "While",
  "Break",
  "Continue",
  "TypeSpec",
  "PList",
};

void PrintNode(FILE *out, struct Node *n, int indent, const char *key) {
  if (n == NULL) {
    fprintf(out, "%*snull\n", indent, "");
    return;
  }

  fprintf(out, "%*s", indent, "");
  indent += key ? strlen(key) : 0;
  if (key) {
    fprintf(out, "%s", key);
  }
  
  fprintf(out, "[%d %s token=", n->index, node_kind_name[n->kind]);
  if (n->token) {
    fprintf(out, "'%.*s'", n->token->len, n->token->raw);
  } else {
    fprintf(out, "(no-token)");
  }
  fprintf(out, " type=");

  if (n->type) {
    PrintType(out, n->type);
  } else {
    fprintf(out, "null");
  }
  if (n->lhs == NULL && n->rhs == NULL && n->cond == NULL) {
    fprintf(out, "]\n");
    if (n->next) {
      PrintNode(out, n->next, indent, NULL);
    }
    return;
  }

  fprintf(out, "\n");
  if (n->lhs) {
    PrintNode(out, n->lhs, indent + 1, "lhs=");
  }
  if (n->cond) {
    PrintNode(out, n->cond, indent + 1, "cond=");
  }
  if (n->rhs) {
    PrintNode(out, n->rhs, indent + 1, "rhs=");
  }
  fprintf(out, "%*s] (%s)\n", indent, "", node_kind_name[n->kind]);

  if (n->next) {
    PrintNode(out, n->next, indent, NULL);
  }
}
