buntan-pc/buntan-pc/dos/apps/buntan_emu.h

unsigned int __builtin_get_sr(unsigned int sr_num) {
  return 0;
}

unsigned int __builtin_set_sr(unsigned int sr_num, unsigned int value) {
  return 0;
}

void __builtin_reset_sr(unsigned int sr_num) {
}
