buntan-pc/buntan-pc/ucc/type.c

// SPDX-License-Identifier: MIT
/*
 * Copyright (c) 2024 Kota UCHIDA
 */
#include "type.h"

#include <stdlib.h>

struct Type *NewType(enum TypeKind kind) {
  struct Type *type = malloc(sizeof(struct Type));
  type->kind = kind;
  type->base = NULL;
  type->next = NULL;
  type->len = 0;
  type->attr = 0;
  return type;
}

struct Type *NewFuncType(struct Type *ret_type, struct Token *id) {
  struct Type *t = NewType(kTypeFunc);
  t->id = id;
  t->base = ret_type;
  return t;
}

size_t SizeofType(struct Type *type) {
  switch (type->kind) {
  case kTypeChar: return 1;
  case kTypeInt: return 2;
  case kTypePtr: return 2;
  case kTypeArray: return type->len * SizeofType(type->base);
  case kTypeVoid: return 0;
  case kTypeEllipsis:
  case kTypeFunc:
    fprintf(stderr, "cannot determine the size: ");
    PrintType(stderr, type);
    fprintf(stderr, "\n");
    exit(1);
  }

  fprintf(stderr, "unknown type: %d\n", type->kind);
  exit(1);
}

void PrintType(FILE *out, struct Type *type) {
  switch (type->kind) {
  case kTypeChar:
    fprintf(out, (type->attr & TYPE_ATTR_SIGNED) ? "signed char" : "char");
    break;
  case kTypeInt:
    fprintf(out, (type->attr & TYPE_ATTR_SIGNED) ? "int" : "unsigned int");
    break;
  case kTypePtr:
    fprintf(out, "*");
    PrintType(out, type->base);
    break;
  case kTypeArray:
    PrintType(out, type->base);
    fprintf(out, "[%d]", type->len);
    break;
  case kTypeVoid:
    fprintf(out, "void");
    break;
  case kTypeEllipsis:
    fprintf(out, "...");
    break;
  case kTypeFunc:
    fprintf(out, "%.*s(", type->id->len, type->id->raw);
    struct Type *param = type->next;
    if (param) {
      PrintType(out, param);
      while ((param = param->next)) {
        fprintf(out, ",");
        PrintType(out, param);
      }
    }
    break;
  }
}
