buntan-pc/buntan-pc/cpu/alu_tb.sv

// SPDX-License-Identifier: MIT
/*
 * Copyright (c) 2024 Kota UCHIDA
 */
`include "common.sv"

module alu_tb;

logic [15:0] a, b;
logic cond;
logic [5:0] sel;
logic [15:0] out;

alu alu(.*);

initial begin
  $monitor("%d: a=%04x b=%04x cond=%d sel=%02x out=%04x",
           $time, a, b, cond, sel, out);

  a <= 16'hDEAD;
  b <= 16'hBEEF;
  cond <= 1'b0;
  sel <= `ALU_A;

  #1 if (out !== 16'hDEAD) $error("out must be 0xDEAD");

  #1 sel <= `ALU_INC;
  #1 if (out !== 16'hDEAE) $error("out must be 0xDEAE");

  #1 sel <= `ALU_INC2;
  #1 if (out !== 16'hDEAF) $error("out must be 0xDEAF");

  #1 sel <= `ALU_INC3;
  #1 if (out !== 16'hDEB0) $error("out must be 0xDEB0");

  // 0xDEAD  = 0b1101_1110_1010_1101
  // ~0xDEAD = 0b0010_0001_0101_0010
  #1 sel <= `ALU_NOT;
  #1 if (out !== 16'h2152) $error("out must be 0x2152");

  #1 sel <= `ALU_SIGN;
  #1 if (out !== 16'h5EAD) $error("out must be 0x5EAD");

  #1 sel <= `ALU_B;
  #1 if (out !== 16'hBEEF) $error("out must be 0xBEEF");

  // 0xDEAD  = 0b1101_1110_1010_1101
  // 0xBEEF  = 0b1011_1110_1110_1111
  #1 sel <= `ALU_AND;
  #1 if (out !== 16'h9EAD) $error("out must be 0x9EAD");

  #1 sel <= `ALU_OR;
  #1 if (out !== 16'hFEEF) $error("out must be 0xFEEF");

  #1 sel <= `ALU_XOR;
  #1 if (out !== 16'h6042) $error("out must be 0x6042");

  #1 sel <= `ALU_SHR; a <= 16'h4;
  #1 if (out !== 16'h0BEE) $error("out must be 0x0BEE");

  #1 sel <= `ALU_SHL;
  #1 if (out !== 16'hEEF0) $error("out must be 0xEEF0");

  #1 sel <= `ALU_SAR;
  #1 if (out !== 16'hFBEE) $error("out must be 0xFBEE");

  #1 a <= 16'd16;
  #1 if (out !== 16'hFFFF) $error("out must be 0xFFFF");

  #1 sel <= `ALU_ADD; a <= 16'h70FF; b <= 16'h2101;
  #1 if (out !== 16'h9200) $error("out must be 0x9200");

  #1 sel <= `ALU_SUB;
  #1 if (out !== 16'hB002) $error("out must be 0xB002");

  #1 sel <= `ALU_MUL;
  #1 if (out !== 16'h4FFF) $error("out must be 0x4FFF");

  #1 sel <= `ALU_EQ;
  #1 if (out !== 16'h0000) $error("out must be 0x0000");

  #1 sel <= `ALU_NEQ;
  #1 if (out !== 16'h0001) $error("out must be 0x0001");

  #1 sel <= `ALU_ADDZ;
  #1 if (out !== 16'h9200) $error("out must be 0x9200"); // 9200 = a+b

  #1 cond <= 1'b1;
  #1 if (out !== 16'h70FF) $error("out must be 0x70FF");

  #1 sel <= `ALU_ADDNZ;
  #1 if (out !== 16'h9200) $error("out must be 0x9200"); // 9200 = a+b

  #1 cond <= 1'b0;
  #1 if (out !== 16'h70FF) $error("out must be 0x70FF");

  a <= 16'hDEAD;
  b <= 16'h0002;

  // b < a  (LT は signed の比較)
  #1 sel <= `ALU_LT;
  #1 if (out !== 16'h0000) $error("out must be 0x0000");

  // b < a  (BT は unsigned の比較)
  #1 sel <= `ALU_BT;
  #1 if (out !== 16'h0001) $error("out must be 0x0001");

  a <= 16'h7FFF;
  b <= 16'h8000;

  #1 sel <= `ALU_LT;
  #1 if (out !== 16'h0001) $error("out must be 0x0001");

  #1 sel <= `ALU_BT;
  #1 if (out !== 16'h0000) $error("out must be 0x0000");
end

endmodule
