buntan-pc/buntan-pc/scripts/append-debuginfo-to-pmem-addr-capture.py

#!/usr/bin/python3

import argparse
from bisect import bisect_right
from collections import namedtuple
from contextlib import nullcontext
import re
import sys
import unittest


ADDRESS_COLUMN_PREFIX = "Parallel:"
AddrLabel = namedtuple("AddrLabel", ["addr", "label"])
Record = namedtuple("Record", ["csv_line", "func", "func_addr", "offset"],
                    defaults=              [ None,           0,        0])
ListLine = namedtuple("ListLine", ["addr", "insn", "src_line_num", "src_line"])
LABEL_PAT = re.compile("^([_a-zA-Z]+):.*$")


def replace_func_name(r, new_func):
    return Record(r.csv_line, new_func, r.func_addr, r.offset)


def load_addr_label_from_map(map_file):
    """
    mapファイルから section .text のラベルだけを読み込む。

    対応するmap形式:

        section .data
        ADDR LABEL
        ----------
        0000 pmem_len
        0002 dmem_len

        section .text
        ADDR LABEL
        ----------
        0000 start
        0002 fin
        0003 buntan_main

    戻り値:
        [
          AddrLabel(0, "start"),
          AddrLabel(2, "fin"),
          AddrLabel(3, "buntan_main")
        ]
    """
    entries = []

    # section .text まで読み飛ばす
    for line in map_file:
        if line.startswith("section .text"):
            break
    # ---- まで読み飛ばす
    for line in map_file:
        if line.startswith("----"):
            break

    for line in map_file:
        line = line.strip()
        parts = line.split()

        if len(parts) != 2:
            raise ValueError("invalid syntax of map line:", line)

        entries.append(AddrLabel(int(parts[0], 16), parts[1]))

    return entries


def split_list_line(line):
    addr = line[0:4]
    insn = line[5:10]
    src_line_num = line[12:17]
    src_line = line[19:].strip()
    return ListLine(addr, insn, src_line_num, src_line)


def load_addr_line_from_list(list_file):
    """
    listファイルからアドレスとソース行の対応を読み込む

    対応するlist形式:

        ADDR  INSN   LINE  FILE_CONTENT
                    00001  section .data
        0004        00002  shift_map:
        ...
                    00156
                    00157  section .text
                    00158  start:
        0000 1601E  00159      push gp+STR_0
        0001 12001  00160      st gp+0
        0002 00BF3  00161      call buntan_main
        0003 10007  00162      st 6
        ...
                    03647  buntan_main:
        0BF6 05D9C  03648      add fp,-612
        ...

    戻り値:
        [
          0000: "    push gp+STR_0",
          0001: "    st gp+0",
          0002: "    call buntan_main",
          0003: "    st 6",
          ...
          0BF6: "    add fp,-612",
          ...
        ]
    """
    addr_lines = []
    list_lines = (split_list_line(line) for line in list_file)

    # section .text まで読み飛ばす
    for line in list_lines:
        if line.src_line.startswith("section .text"):
            break

    for line in list_lines:
        addr = line.addr.strip()
        if not addr:
            continue

        addr_hex = int(addr, 16)
        if len(addr_lines) < addr_hex + 1:
            addr_lines.extend([None] * (addr_hex - len(addr_lines)))
            addr_lines.append(line.src_line)
        else:
            addr_lines[addr_hex] = line.src_line

    return addr_lines


def find_current_function(addr: int, addrlabels: list) -> (int, str):
    """
    addr 以下で最も近いラベルを返す。配列の添字とラベルを返す。

    例:
        map:
            0000 start
            0002 fin
            0003 buntan_main

        addr=0000 -> 0, start
        addr=0001 -> 0, start
        addr=0002 -> 1, fin
        addr=0003 -> 2, buntan_main
        addr=0004 -> 2, buntan_main
    """
    index = bisect_right(addrlabels, addr, key=lambda x: x.addr) - 1
    if index < 0:
        return -1, ""
    return index, addrlabels[index].label


def add_debug_column(csv_file, addrlabels: list[AddrLabel], func_entry_only) -> list[Record]:
    for line in csv_file:
        line = line.rstrip()
        # line: index,time,pmem_addr
        comma = line.rfind(",")
        # 観測される addr は実行中命令の次を指すので、
        # 実行中命令のアドレスを求めるために 1 を引く
        addr = int(line[comma+1:], 16) - 1
        ind, func = find_current_function(addr, addrlabels)
        func_addr = addrlabels[ind].addr
        if func_entry_only and func_addr != addr:
            continue
        yield Record(line, func, func_addr, addr - func_addr)


def unique(records: list[Record]) -> list[Record]:
    prev_rec = next(records)
    rep_cnt = 1
    for r in records:
        if prev_rec.func == r.func:
            rep_cnt += 1
            continue
        else:
            if rep_cnt >= 2:
                yield replace_func_name(prev_rec, prev_rec.func + f" [x{rep_cnt}]")
            else:
                yield prev_rec
            prev_rec = r
            rep_cnt = 1

    if rep_cnt >= 2:
        yield replace_func_name(prev_rec, prev_rec.func + f" [x{rep_cnt}]")
    else:
        yield prev_rec


class TestUnique(unittest.TestCase):

    def test_ends_with_repeats(self):
        records = (Record(f"{i},2", func) for i, func in enumerate("abbbccc"))
        want = [
            Record("0,2", "a"),
            Record("1,2", "b [x3]"),
            Record("4,2", "c [x3]"),
        ]
        self.assertEqual(want, list(unique(records)))

    def test_ends_with_single(self):
        records = (Record(f"{i},2", func) for i, func in enumerate("abbbcccd"))
        want = [
            Record("0,2", "a"),
            Record("1,2", "b [x3]"),
            Record("4,2", "c [x3]"),
            Record("7,2", "d"),
        ]
        self.assertEqual(want, list(unique(records)))



def collapse_repeats(records: list[Record]) -> list[Record]:
    pattern = []  # [Record]
    repeat_candidate = []  # [Record]
    repeat_count = -1

    for r in records:
        if len(pattern) == 0:
            pattern.append(r)
            continue

        if repeat_count == -1:
            func_i = next(
                (i for i, elem in enumerate(pattern) if elem.func == r.func),
                -1
            )
            if func_i >= 0:
                # 繰り返しが始まった可能性
                for rec in pattern[:func_i]:
                    yield rec
                pattern = pattern[func_i:]
                if len(pattern) == 1 and pattern[0].func == r.func:
                    repeat_candidate = []
                    repeat_count = 1
                else:
                    repeat_candidate = [r]
                    repeat_count = 0
            else:
                if len(pattern) == 20:
                    yield pattern[0]
                    pattern.pop(0)
                pattern.append(r)
        elif repeat_count >= 0:
            if pattern[len(repeat_candidate)].func == r.func:
                # まだ繰り返しの可能性が続いている
                repeat_candidate.append(r)
                if len(pattern) == len(repeat_candidate):
                    repeat_candidate = []
                    repeat_count += 1
            elif repeat_count == 0:
                # 結局、繰り返しは無かった
                for rec in pattern:
                    yield rec
                pattern = repeat_candidate
                pattern.append(r)
                repeat_candidate = []
                repeat_count = -1
            else: # repeat_count >= 1
                # 繰り返しが終わった
                if len(pattern) == 1:
                    yield replace_func_name(pattern[0], pattern[0].func + f" [x{repeat_count+1}]")
                else:
                    yield Record(f"[repeat x{repeat_count+1} total]")
                    for rec in pattern:
                        yield rec
                    yield Record("[/repeat]")

                for rec in repeat_candidate:
                    yield rec
                repeat_candidate = []
                pattern = [r]
                repeat_count = -1

    if repeat_count >= 0:
        yield Record(f"[repeat x{repeat_count+1} total]")
    for rec in pattern:
        yield rec
    if repeat_count >= 0:
        yield Record(f"[/repeat]")
    for rec in repeat_candidate:
        yield rec


class TestCollapseRepeats(unittest.TestCase):

    def test_true_candidate(self):
        records = [Record(f"{i},2", func) for i, func in enumerate("abababcdefefef")]
        want = [
            Record("[repeat x3 total]", None),
            Record("0,2", "a"),
            Record("1,2", "b"),
            Record("[/repeat]", None),
            Record("6,2", "c"),
            Record("7,2", "d"),
            Record("[repeat x3 total]", None),
            Record("8,2", "e"),
            Record("9,2", "f"),
            Record("[/repeat]", None),
        ]
        self.assertEqual(want, list(collapse_repeats(records)))

    def test_false_repeat_candidate(self):
        records = [Record(f"{i},2", func) for i, func in enumerate("abcdcecef")]
        want = [
            Record("0,2", "a"),
            Record("1,2", "b"),
            Record("2,2", "c"),
            Record("3,2", "d"),
            Record("[repeat x2 total]", None),
            Record("4,2", "c"),
            Record("5,2", "e"),
            Record("[/repeat]", None),
            Record("8,2", "f"),
        ]
        self.assertEqual(want, list(collapse_repeats(records)))

    def test_endswith_repeat(self):
        records = [Record(f"{i},2", func) for i, func in enumerate("abab")]
        want = [
            Record("[repeat x2 total]", None),
            Record("0,2", "a"),
            Record("1,2", "b"),
            Record("[/repeat]", None),
        ]
        self.assertEqual(want, list(collapse_repeats(records)))

    def test_endswith_candidate(self):
        records = [Record(f"{i},2", func) for i, func in enumerate("ababa")]
        want = [
            Record("[repeat x2 total]", None),
            Record("0,2", "a"),
            Record("1,2", "b"),
            Record("[/repeat]", None),
            Record("4,2", "a"),
        ]
        self.assertEqual(want, list(collapse_repeats(records)))

    def test_repeat_printing(self):
        records = [Record(f"{i},2", func) for i, func in enumerate("aaab")]
        want = [
            Record("0,2", "a [x3]"),
            Record("3,2", "b"),
        ]
        self.assertEqual(want, list(collapse_repeats(records)))


def main():
    parser = argparse.ArgumentParser(
        description="""\
ロジックアナライザで記録した CSV 中の pmem アドレスに対応する関数名を追加する。
CSV ファイルのフォーマット：
    Id,Time[ns],Parallel: Items
    1,20.00,F1E
    2,160.00,018
    3,300.00,019

"Parallel: Items|Words" が pmem アドレスである。

pmem アドレスから関数名を特定するために list ファイルを利用する。
list ファイルのフォーマット：
    ADDR  INSN   LINE  FILE_CONTENT
                00001  section .data
    0004        00002  shift_map:
    ...
                00156
                00157  section .text
                00158  start:
    0000 1601E  00159      push gp+STR_0
    0001 12001  00160      st gp+0
    ...
""",
        formatter_class=argparse.RawDescriptionHelpFormatter
    )

    parser.add_argument("csv", help="入力 CSV ファイル")
    parser.add_argument("map", help="uas 出力の map ファイル")
    parser.add_argument("lst", help="uas 出力の list ファイル")
    parser.add_argument("-o", "--output", help="出力 CSV ファイル")
    parser.add_argument("--func-entry-only", action="store_true",
                        help="関数先頭の行だけを残す")
    parser.add_argument("--collapse-repeats", action="store_true",
                        help="同じ関数の組が連続する区間を省略する")

    args = parser.parse_args()

    with open(args.map) as f:
        addrlabels = load_addr_label_from_map(f)
    with open(args.lst) as f:
        addrlines = load_addr_line_from_list(f)

    def open_or_use(file_path, open_mode, file_obj):
        if file_path and file_path != "-":
            return open(file_path, open_mode)
        return nullcontext(file_obj)

    with open_or_use(args.csv, "r", sys.stdin) as csv_file, \
         open_or_use(args.output, "w", sys.stdout) as out_file:
        header = csv_file.readline().strip()
        fieldnames = header.split(",")

        for fieldname in fieldnames:
            if fieldname.startswith(ADDRESS_COLUMN_PREFIX):
                break
        else:
            raise RuntimeError(f"CSVに '{ADDRESS_COLUMN_PREFIX}' 列が見つかりません。")

        out_file.write("Id,Time[ns],Addr,Function,FAdr,FOff,SrcLine\n")

        records = add_debug_column(csv_file, addrlabels, args.func_entry_only)
        if args.collapse_repeats:
            records = unique(records)
            records = collapse_repeats(records)

        for r in records:
            addr = r.func_addr + r.offset
            out_file.write(r.csv_line
                           + ("," + r.func if r.func else ",,,")
                           + f",{r.func_addr:04X}"
                           + f",{r.offset:04X}"
                           + f",{addrlines[addr]}"
                           + "\n")


if __name__ == "__main__":
    main()
