buntan-pc/buntan-pc/cpu/verilator/sim_top.sv

`include "common.sv"

module sim_top#(
  parameter CLOCK_HZ = 27_000_000
) (
  input rst, clk, uart_rx, uart2_rx, uart3_rx,
  input  [7:0] uart_in_data,
  input  uart_in_wr,
  output uart_tx, uart2_tx, uart3_tx,
  output uart_in_ready,
  output [`ADDR_WIDTH-1:0] dmem_addr,
  output dmem_wen, dmem_byt,
  input  [15:0] dmem_rdata_io,
  output [15:0] dmem_wdata,
  output [17:0] uart_recv_data,
  output [`ADDR_WIDTH-1:0] img_pmem_size,
  input  clk125,
  input  adc_cmp,
  output adc_sh_ctl,
  output adc_dac_pwm,
  output [8:0] uf_xadr,
  output [5:0] uf_yadr,
  output uf_xe, uf_ye, uf_se, uf_erase, uf_prog, uf_nvstr,
  output [31:0] uf_din,
  input  [31:0] uf_dout,
  output spi_cs,
  output spi_sclk, spi_mosi,
  input  spi_miso,
  inout  [7:0] key_col_n,
  output [7:0] key_row,
  inout  i2c_scl, i2c_sda,
  output dbgio,
  output [7:0] uart_out_data,
  output uart_out_full
);

localparam UART_BAUD = CLOCK_HZ / 10;
logic mcu_uart_rx;

mcu #(
  .CLOCK_HZ(CLOCK_HZ),
  .UART_BAUD(UART_BAUD)
) mcu(
  .*,
  .uart_rx(mcu_uart_rx)
);

uart #(
  .CLOCK_HZ(CLOCK_HZ),
  .BAUD(UART_BAUD)
) uart_in_encoder(
  .rst(rst),
  .clk(clk),
  .rx(1'b1),
  .tx(mcu_uart_rx),
  .rx_data(),
  .tx_data(uart_in_data),
  .rd(1'b0),
  .rx_full(),
  .wr(uart_in_wr),
  .tx_ready(uart_in_ready)
);

uart #(
  .CLOCK_HZ(CLOCK_HZ),
  .BAUD(UART_BAUD)
) uart_out_decoder(
  .rst(rst),
  .clk(clk),
  .rx(uart_tx),
  .tx(),
  .rx_data(uart_out_data),
  .tx_data(8'hff),
  .rd(uart_out_full),
  .rx_full(uart_out_full),
  .wr(1'b0),
  .tx_ready()
);

endmodule
